nishil-26/arc32-sdk/hardware/arc32_v1_neo/source_kicad/arc32_v1_neo.kicad_sch

## KiCad design hardware/arc32_v1_neo/source_kicad/arc32_v1_neo.kicad_sch (2026-07-04)

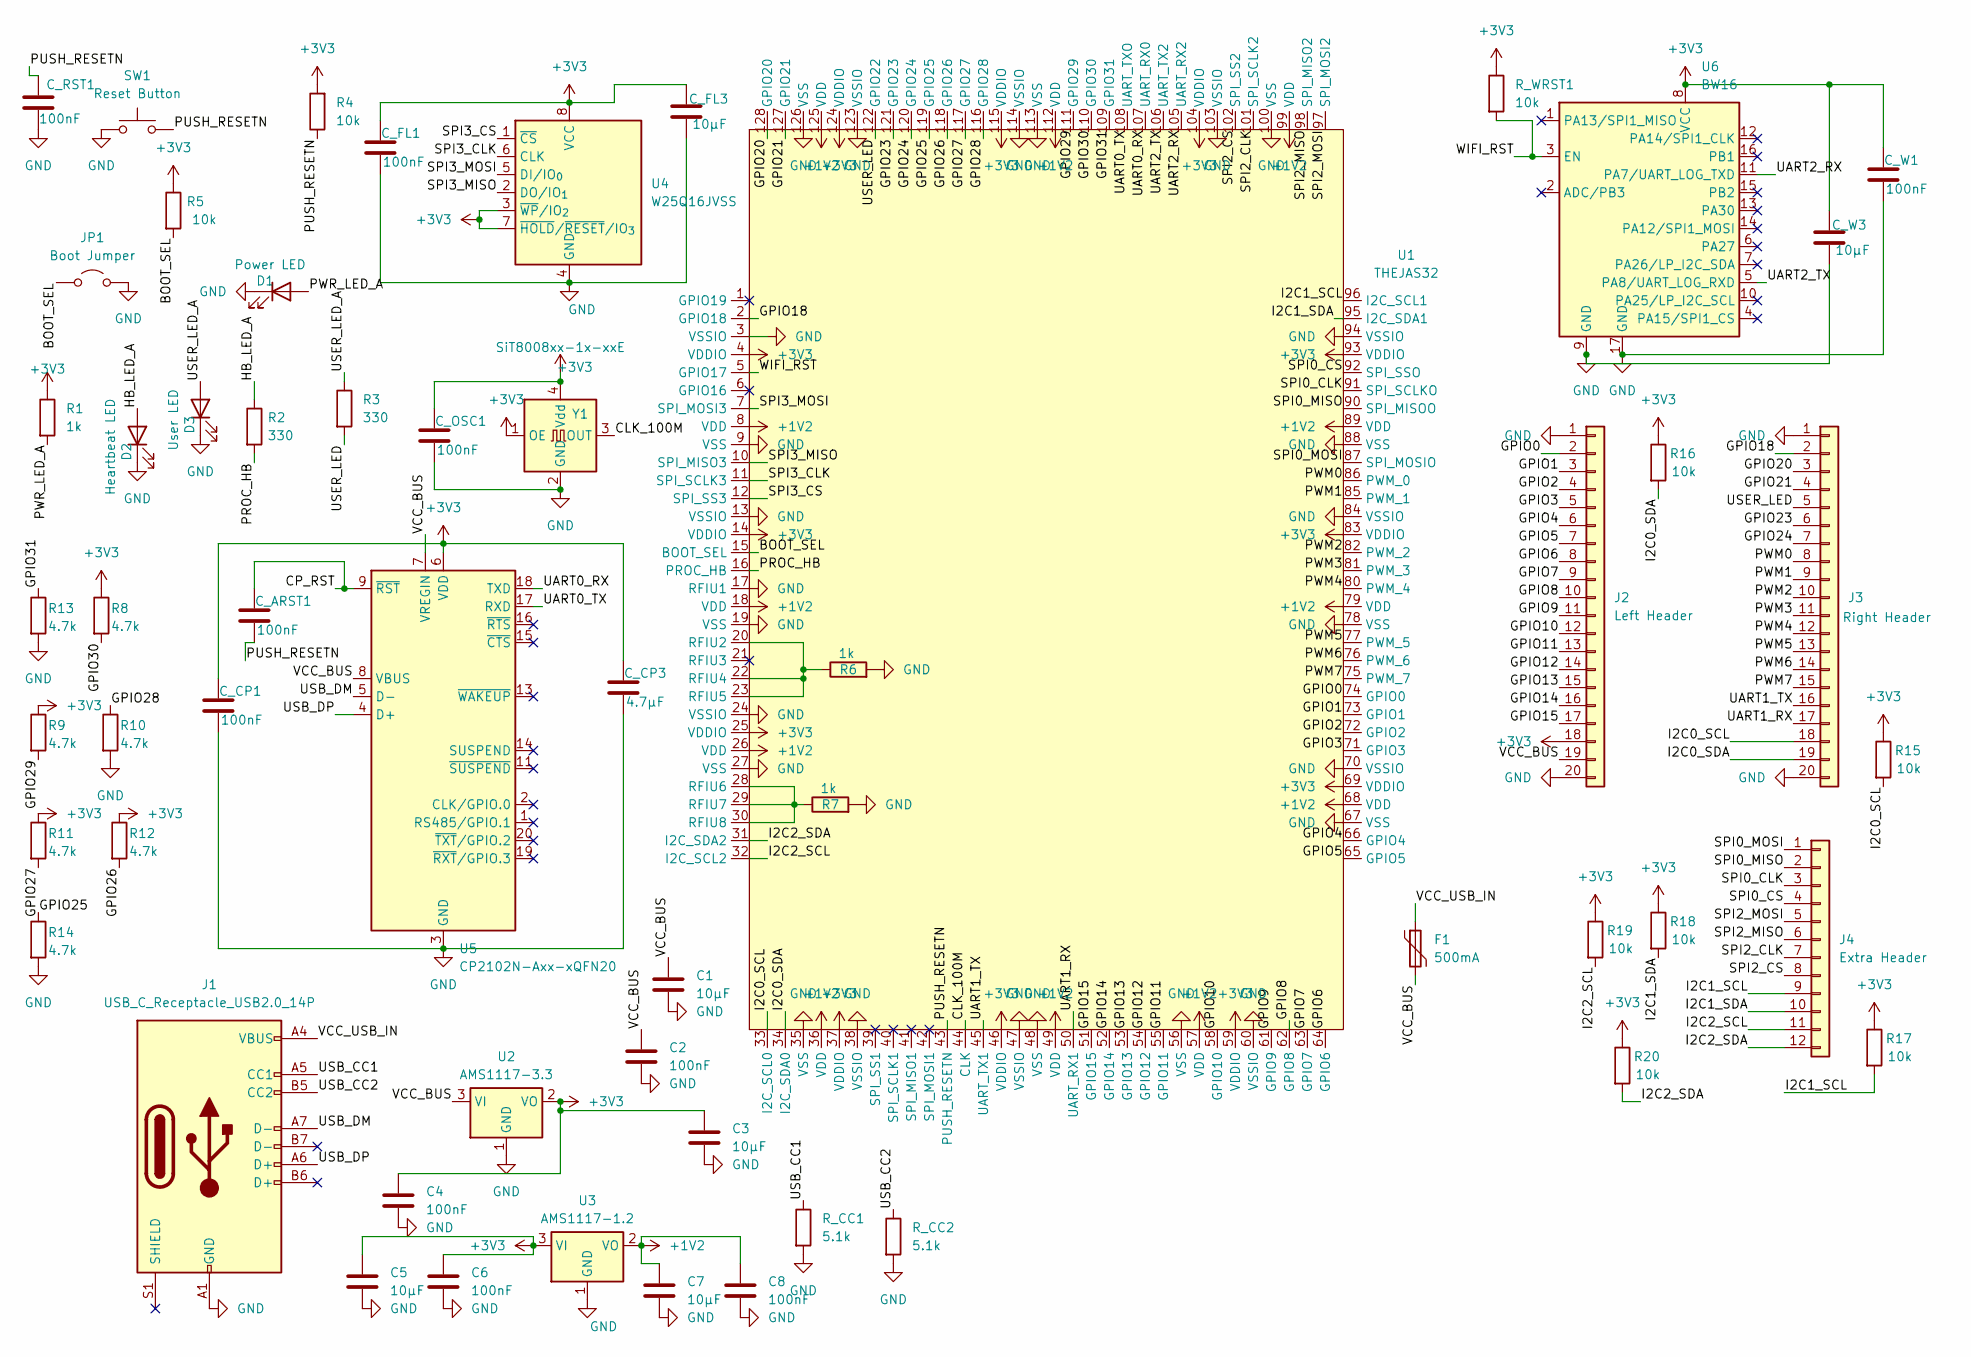
[picture p5: schematic arc32_v1_neo.kicad_sch]

Parts:
C1, C3, C5, C7: 10µF; C_0805_2012Metric
C2, C4, C6, C8: 100nF; C_0805_2012Metric
C_ARST1: 100nF; C_0805_2012Metric
C_CP1: 100nF; C_0805_2012Metric
C_CP3: 4.7µF; C_0805_2012Metric
C_FL1: 100nF; C_0805_2012Metric
C_FL3: 10µF; C_0805_2012Metric
C_OSC1: 100nF; C_0805_2012Metric
C_RST1: 100nF; C_0805_2012Metric
C_W1: 100nF; C_0805_2012Metric
C_W3: 10µF; C_0805_2012Metric
D1: Power LED; LED_0603_1608Metric
D2: Heartbeat LED; LED_0603_1608Metric
D3: User LED; LED_0603_1608Metric
F1: 500mA; Fuse_1206_3216Metric
J1: USB_C_Receptacle_USB2.0_14P; USB_C_Receptacle_HRO_TYPE-C-31-M-12
J2: Left Header; PinHeader_1x20_P2.54mm_Vertical_SMD_Pin1Left
J3: Right Header; PinHeader_1x20_P2.54mm_Vertical_SMD_Pin1Right
J4: Extra Header; PinHeader_1x12_P2.54mm_Vertical
JP1: Boot Jumper; SolderJumper-2_P1.3mm_Open_TrianglePad1.0x1.5mm
R1, R6, R7: 1k; R_0603_1608Metric
R2, R3: 330; R_0603_1608Metric
R4, R5, R15, R16, R17, R18, R19, R20: 10k; R_0603_1608Metric
R8, R9, R10, R11, R12, R13, R14: 4.7k; R_0603_1608Metric
R_CC1, R_CC2: 5.1k; R_0603_1608Metric
R_WRST1: 10k; R_0603_1608Metric
SW1: Reset Button; SW_SPST_TL3342
U1: THEJAS32; LQFP-128_14x14mm_P0.4mm
U2: AMS1117-3.3; SOT-223-3_TabPin2
U3: AMS1117-1.2; SOT-223-3_TabPin2
U4: W25Q16JVSS; SOIC-8_5.3x5.3mm_P1.27mm
U5: CP2102N-Axx-xQFN20; QFN-20-1EP_3x3mm_P0.4mm_EP1.65x1.65mm
U6: BW16
Y1: SiT8008xx-1x-xxE; Oscillator_SMD_SiT_PQFN-4Pin_2.5x2.0mm

Connections:
+1V2: C7.1, C8.1, U1.8 (VDD), U1.18 (VDD), U1.26 (VDD), U1.36 (VDD), U1.49 (VDD), U1.57 (VDD), U1.68 (VDD), U1.79 (VDD), U1.89 (VDD), U1.99 (VDD), U1.112 (VDD), U1.125 (VDD), U3.2 (VO)
+3V3: C3.1, C4.1, C5.1, C6.1, C_CP1.1, C_CP3.1, C_FL1.1, C_FL3.1, C_OSC1.1, C_W1.1, C_W3.1, J2.18, R1.1, R4.2, R5.1, R8.1, R9.1, R11.1, R12.1, R15.1, R16.1, R17.1, R18.1, R19.1, R20.1, R_WRST1.1, U1.4 (VDDIO), U1.14 (VDDIO), U1.25 (VDDIO), U1.37 (VDDIO), U1.46 (VDDIO), U1.59 (VDDIO), U1.69 (VDDIO), U1.83 (VDDIO), U1.93 (VDDIO), U1.104 (VDDIO), U1.115 (VDDIO), U1.124 (VDDIO), U2.2 (VO), U3.3 (VI), U4.3 (~WP/IO_{2}), U4.7 (~HOLD/~RESET/IO_{3}), U4.8 (VCC), U5.6 (VDD), U6.8 (VCC), Y1.1 (OE), Y1.4 (Vdd)
BOOT_SEL: JP1.1 (A), R5.2, U1.15 (BOOT_SEL)
CLK_100M: U1.44 (CLK), Y1.3 (OUT)
CP_RST: C_ARST1.1, U5.9 (~RST)
GND: C1.2, C2.2, C3.2, C4.2, C5.2, C6.2, C7.2, C8.2, C_CP1.2, C_CP3.2, C_FL1.2, C_FL3.2, C_OSC1.2, C_RST1.2, C_W1.2, C_W3.2, D1.1 (K), D2.1 (K), D3.1 (K), J1.A1 (GND), J1.A12 (GND), J1.B1 (GND), J1.B12 (GND), J2.1, J2.20, J3.1, J3.20, JP1.2 (B), R6.2, R7.2, R10.2, R13.2, R14.2, R_CC1.2, R_CC2.2, SW1.1, U1.3 (VSSIO), U1.9 (VSS), U1.13 (VSSIO), U1.17 (RFIU1), U1.19 (VSS), U1.24 (VSSIO), U1.27 (VSS), U1.35 (VSS), U1.38 (VSSIO), U1.47 (VSSIO), U1.48 (VSS), U1.56 (VSS), U1.60 (VSSIO), U1.67 (VSS), U1.70 (VSSIO), U1.78 (VSS), U1.84 (VSSIO), U1.88 (VSS), U1.94 (VSSIO), U1.100 (VSS), U1.103 (VSSIO), U1.113 (VSS), U1.114 (VSSIO), U1.123 (VSSIO), U1.126 (VSS), U2.1 (GND), U3.1 (GND), U4.4 (GND), U5.3 (GND), U5.12 (GND), U5.21 (GND), U6.9 (GND), U6.17 (GND), Y1.2 (GND)
GPIO0: J2.2, U1.74 (GPIO0)
GPIO1: J2.3, U1.73 (GPIO1)
GPIO2: J2.4, U1.72 (GPIO2)
GPIO3: J2.5, U1.71 (GPIO3)
GPIO4: J2.6, U1.66 (GPIO4)
GPIO5: J2.7, U1.65 (GPIO5)
GPIO6: J2.8, U1.64 (GPIO6)
GPIO7: J2.9, U1.63 (GPIO7)
GPIO8: J2.10, U1.62 (GPIO8)
GPIO9: J2.11, U1.61 (GPIO9)
GPIO10: J2.12, U1.58 (GPIO10)
GPIO11: J2.13, U1.55 (GPIO11)
GPIO12: J2.14, U1.54 (GPIO12)
GPIO13: J2.15, U1.53 (GPIO13)
GPIO14: J2.16, U1.52 (GPIO14)
GPIO15: J2.17, U1.51 (GPIO15)
GPIO18: J3.2, U1.2 (GPIO18)
GPIO20: J3.3, U1.128 (GPIO20)
GPIO21: J3.4, U1.127 (GPIO21)
GPIO23: J3.6, U1.121 (GPIO23)
GPIO24: J3.7, U1.120 (GPIO24)
GPIO25: R14.1, U1.119 (GPIO25)
GPIO26: R12.2, U1.118 (GPIO26)
GPIO27: R11.2, U1.117 (GPIO27)
GPIO28: R10.1, U1.116 (GPIO28)
GPIO29: R9.2, U1.111 (GPIO29)
GPIO30: R8.2, U1.110 (GPIO30)
GPIO31: R13.1, U1.109 (GPIO31)
HB_LED_A: D2.2 (A), R2.1
I2C0_SCL: J3.18, R15.2, U1.33 (I2C_SCL0)
I2C0_SDA: J3.19, R16.2, U1.34 (I2C_SDA0)
I2C1_SCL: J4.9, R17.2, U1.96 (I2C_SCL1)
I2C1_SDA: J4.10, R18.2, U1.95 (I2C_SDA1)
I2C2_SCL: J4.11, R19.2, U1.32 (I2C_SCL2)
I2C2_SDA: J4.12, R20.2, U1.31 (I2C_SDA2)
unnamed: R6.1, U1.20 (RFIU2), U1.22 (RFIU4), U1.23 (RFIU5)
unnamed: R7.1, U1.28 (RFIU6), U1.29 (RFIU7), U1.30 (RFIU8)
PROC_HB: R2.2, U1.16 (PROC_HB)
PUSH_RESETN: C_ARST1.2, C_RST1.1, R4.1, SW1.2, U1.43 (PUSH_RESETN)
PWM0: J3.8, U1.86 (PWM_0)
PWM1: J3.9, U1.85 (PWM_1)
PWM2: J3.10, U1.82 (PWM_2)
PWM3: J3.11, U1.81 (PWM_3)
PWM4: J3.12, U1.80 (PWM_4)
PWM5: J3.13, U1.77 (PWM_5)
PWM6: J3.14, U1.76 (PWM_6)
PWM7: J3.15, U1.75 (PWM_7)
PWR_LED_A: D1.2 (A), R1.2
SPI0_CLK: J4.3, U1.91 (SPI_SCLKO)
SPI0_CS: J4.4, U1.92 (SPI_SSO)
SPI0_MISO: J4.2, U1.90 (SPI_MISOO)
SPI0_MOSI: J4.1, U1.87 (SPI_MOSIO)
SPI2_CLK: J4.7, U1.101 (SPI_SCLK2)
SPI2_CS: J4.8, U1.102 (SPI_SS2)
SPI2_MISO: J4.6, U1.98 (SPI_MISO2)
SPI2_MOSI: J4.5, U1.97 (SPI_MOSI2)
SPI3_CLK: U1.11 (SPI_SCLK3), U4.6 (CLK)
SPI3_CS: U1.12 (SPI_SS3), U4.1 (~CS)
SPI3_MISO: U1.10 (SPI_MISO3), U4.2 (DO/IO_{1})
SPI3_MOSI: U1.7 (SPI_MOSI3), U4.5 (DI/IO_{0})
UART0_RX: U1.107 (UART_RX0), U5.18 (TXD)
UART0_TX: U1.108 (UART_TXO), U5.17 (RXD)
UART1_RX: J3.17, U1.50 (UART_RX1)
UART1_TX: J3.16, U1.45 (UART_TX1)
UART2_RX: U1.105 (UART_RX2), U6.11 (PA7/UART_LOG_TXD)
UART2_TX: U1.106 (UART_TX2), U6.5 (PA8/UART_LOG_RXD)
USB_CC1: J1.A5 (CC1), R_CC1.1
USB_CC2: J1.B5 (CC2), R_CC2.1
USB_DM: J1.A7 (D-), U5.5 (D-)
USB_DP: J1.A6 (D+), U5.4 (D+)
USER_LED: J3.5, R3.2, U1.122 (GPIO22)
USER_LED_A: D3.2 (A), R3.1
VCC_BUS: C1.1, C2.1, F1.2, J2.19, U2.3 (VI), U5.7 (VREGIN), U5.8 (VBUS)
VCC_USB_IN: F1.1, J1.A4 (VBUS), J1.A9 (VBUS), J1.B4 (VBUS), J1.B9 (VBUS)
WIFI_RST: R_WRST1.2, U1.5 (GPIO17), U6.3 (EN)
